dieseltravis/travis-ergogen-2026/datasheets/mcu-Liatris-rev1.0.webp

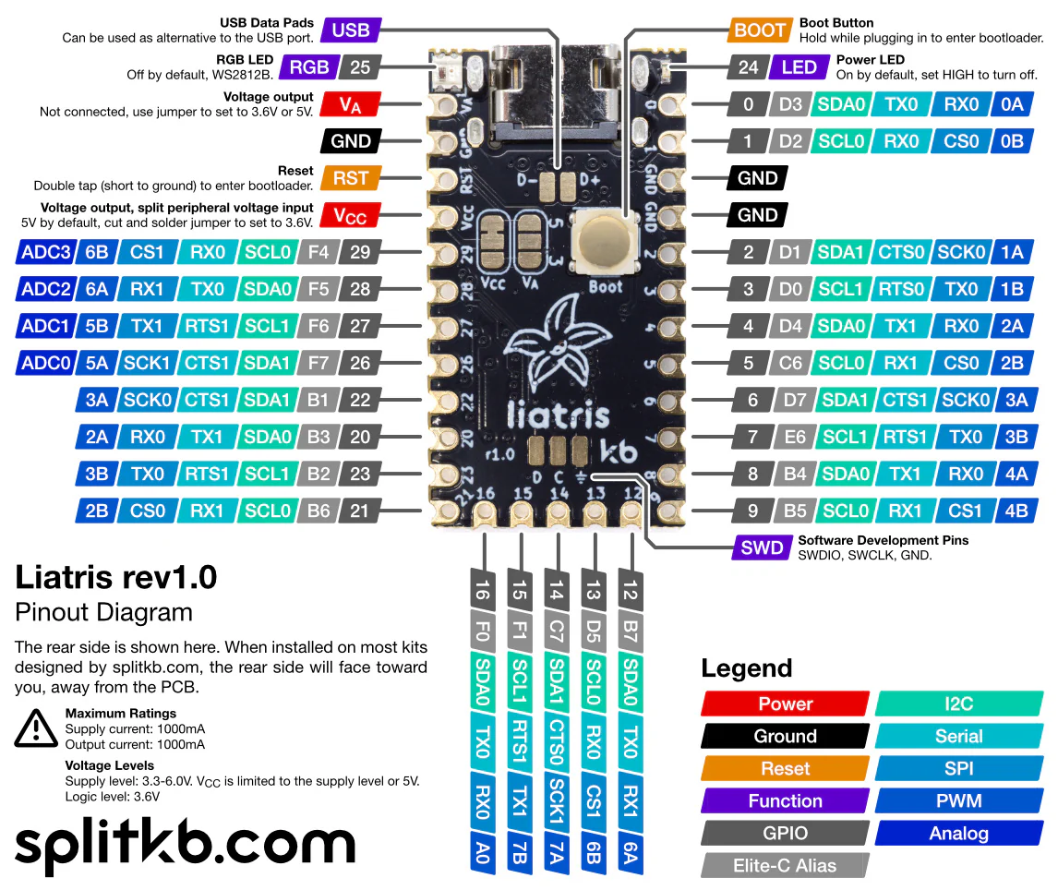
datasheets/mcu-Liatris-rev1.0.webp
