dieseltravis/travis-ergogen-2026/output/outlines/_2u_stabilizer.dxf

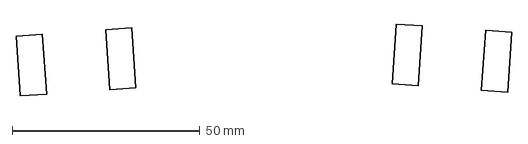
[picture p21: CAD file, 2026-01-18]
output/outlines/_2u_stabilizer.dxf
132.0 x 19.2 mm
