dieseltravis/travis-ergogen-2026/output/outlines/_keys.dxf

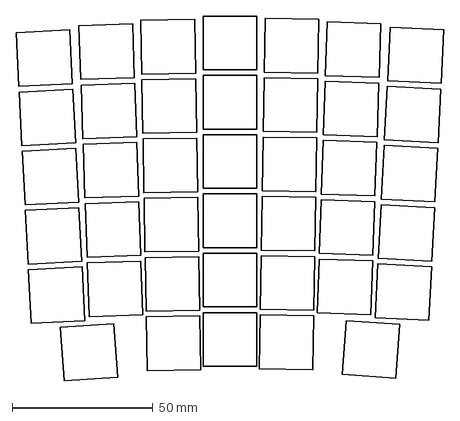
[picture p22: CAD file, 2026-01-15]
output/outlines/_keys.dxf
151.8 x 129.5 mm
