dieseltravis/travis-ergogen-2026/output/points/points.yaml

matrix_col0_row0:
    x: 60.0112611
    'y': -199.475332
    r: 4
    meta:
        stagger: 0
        spread: 20.05
        splay: 3
        origin:
            - 0
            - 0
        orient: 0
        shift:
            - 10.025
            - 0
        rotate: 1
        adjust: {}
        width: 38.1
        height: 18
        padding: 21.05
        autobind: 10
        skip: false
        asym: both
        colrow: col0_row0
        name: matrix_col0_row0
        tags:
            - row_even
            - key
            - 2u_stabs
        column_net: col0
        row_net: row0
        key:
            led_next: LED37
            led_this: LED36
        zone:
            key:
                padding: kp
                spread: kspr
                tags:
                    - key
            columns:
                col0:
                    key:
                        tags: col_even
                        splay: 3sp
                        stagger: 0st
                        column_net: col0
                    rows:
                        row0:
                            shift:
                                - 0.5kspr
                                - 0.0kp
                            width: 2U
                            rotate: 1
                            tags:
                                - row_even
                                - key
                                - 2u_stabs
                            key:
                                led_next: LED37
                                led_this: LED36
                        row1:
                            shift:
                                - '-0.5kspr'
                                - 0.0kp
                            rotate: -1
                            key:
                                led_next: LED36
                                led_this: LED35
                        row2:
                            key:
                                led_next: LED23
                                led_this: LED22
                        row3:
                            key:
                                led_next: LED22
                                led_this: LED21
                        row4:
                            key:
                                led_next: LED09
                                led_this: LED08
                        row5:
                            key:
                                led_next: LED08
                                led_this: LED07
                    name: col0
                col1:
                    key:
                        tags: col_odd
                        splay: '-sp'
                        stagger: st
                        column_net: col1
                    rows:
                        row0:
                            skip: true
                        row1:
                            key:
                                led_next: LED35
                                led_this: LED34
                        row2:
                            key:
                                led_next: LED24
                                led_this: LED23
                        row3:
                            key:
                                led_next: LED21
                                led_this: LED20
                        row4:
                            key:
                                led_next: LED10
                                led_this: LED09
                        row5:
                            key:
                                led_next: LED07
                                led_this: LED06
                    name: col1
                col2:
                    key:
                        tags: col_even
                        splay: '-sp'
                        stagger: st
                        column_net: col2
                    rows:
                        row0:
                            key:
                                led_next: LED38
                                led_this: LED37
                        row1:
                            key:
                                led_next: LED34
                                led_this: LED33
                        row2:
                            key:
                                led_next: LED25
                                led_this: LED24
                        row3:
                            key:
                                led_next: LED20
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
                    shift:
                        - '-0.5kspr'
                        - 0.0kp
                    rotate: -1
                    key:
                        led_next: LED36
                        led_this: LED35
                row2:
                    key:
                        led_next: LED23
                        led_this: LED22
                row3:
                    key:
                        led_next: LED22
                        led_this: LED21
                row4:
                    key:
                        led_next: LED09
                        led_this: LED08
                row5:
                    key:
                        led_next: LED08
                        led_this: LED07
            name: col0
        row: row0
        bind:
            - 10
            - 0
            - 0
            - 0
matrix_col0_row1:
    x: 48.542307699999995
    'y': -179.1759173
    r: 3
    meta:
        stagger: 0
        spread: 20.05
        splay: 3
        origin:
            - 0
            - 0
        orient: 0
        shift:
            - -10.025
            - 0
        rotate: -1
        adjust: {}
        width: 18
        height: 18
        padding: 21.05
        autobind: 10
        skip: false
        asym: both
        colrow: col0_row1
        name: matrix_col0_row1
        tags:
            - key
            - row_odd
        column_net: col0
        row_net: row1
        key:
            led_next: LED36
            led_this: LED35
        zone:
            key:
                padding: kp
                spread: kspr
                tags:
                    - key
            columns:
                col0:
                    key:
                        tags: col_even
                        splay: 3sp
                        stagger: 0st
                        column_net: col0
                    rows:
                        row0:
                            shift:
                                - 0.5kspr
                                - 0.0kp
                            width: 2U
                            rotate: 1
                            tags:
                                - row_even
                                - key
                                - 2u_stabs
                            key:
                                led_next: LED37
                                led_this: LED36
                        row1:
                            shift:
                                - '-0.5kspr'
                                - 0.0kp
                            rotate: -1
                            key:
                                led_next: LED36
                                led_this: LED35
                        row2:
                            key:
                                led_next: LED23
                                led_this: LED22
                        row3:
                            key:
                                led_next: LED22
                                led_this: LED21
                        row4:
                            key:
                                led_next: LED09
                                led_this: LED08
                        row5:
                            key:
                                led_next: LED08
                                led_this: LED07
                    name: col0
                col1:
                    key:
                        tags: col_odd
                        splay: '-sp'
                        stagger: st
                        column_net: col1
                    rows:
                        row0:
                            skip: true
                        row1:
                            key:
                                led_next: LED35
                                led_this: LED34
                        row2:
                            key:
                                led_next: LED24
                                led_this: LED23
                        row3:
                            key:
                                led_next: LED21
                                led_this: LED20
                        row4:
                            key:
                                led_next: LED10
                                led_this: LED09
                        row5:
                            key:
                                led_next: LED07
                                led_this: LED06
                    name: col1
                col2:
                    key:
                        tags: col_even
                        splay: '-sp'
                        stagger: st
                        column_net: col2
                    rows:
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
                        row4:
                            key:
                                led_next: LED14
                                led_this: LED13
                        row5:
                            key:
                                led_next: LED03
                                led_this: LED02
                    name: col5
                col6:
                    key:
                        tags: col_even
                        splay: '-sp'
                        stagger: '-st'
                        column_net: col6
                    rows:
                        row0:
                            shift:
                                - '-0.5kspr'
                                - 0.0kp
                            width: 2U
                            rotate: -1
                            tags:
                                - row_even
                                - key
                                - 2u_stabs
                            key:
                                led_next: ''
                                led_this: LED40
                        row1:
                            shift:
                                - 0.5kspr
                                - 0.0kp
                            rotate: 1
                            key:
                                led_next: LED30
                                led_this: LED29
                        row2:
                            key:
                                led_next: LED29
                                led_this: LED28
                        row3:
                            key:
                                led_next: LED16
                                led_this: LED15
                        row4:
                            key:
                                led_next: LED15
                                led_this: LED14
                        row5:
                            key:
                                led_next: LED02
                                led_this: LED01
                    name: col6
            rows:
                row0:
                    tags:
                        - key
                        - row_even
                    row_net: row0
                row1:
                    tags:
                        - key
                        - row_odd
                    row_net: row1
                row2:
                    tags:
                        - key
                        - row_even
                    row_net: row2
                row3:
                    tags:
                        - key
                        - row_odd
                    row_net: row3
                row4:
                    tags:
                        - key
                        - row_even
                    row_net: row4
                row5:
                    tags:
                        - key
                        - row_odd
                    row_net: row5
            name: matrix
        col:
            key:
                tags: col_even
                splay: 3sp
                stagger: 0st
                column_net: col0
            rows:
                row0:
                    shift:
                        - 0.5kspr
                        - 0.0kp
                    width: 2U
                    rotate: 1
                    tags:
                        - row_even
                        - key
                        - 2u_stabs
                    key:
                        led_next: LED37
                        led_this: LED36
                row1:
                    shift:
                        - '-0.5kspr'
                        - 0.0kp
                    rotate: -1
                    key:
                        led_next: LED36
                        led_this: LED35
                row2:
                    key:
                        led_next: LED23
                        led_this: LED22
                row3:
                    key:
                        led_next: LED22
                        led_this: LED21
                row4:
                    key:
                        led_next: LED09
                        led_this: LED08
                row5:
                    key:
                        led_next: LED08
                        led_this: LED07
            name: col0
        row: row1
        bind:
            - 10
            - 0
            - 10
            - 0
matrix_col0_row2:
    x: 47.440635799999995
    'y': -158.15476560000002
    r: 3
    meta:
        stagger: 0
        spread: 20.05
        splay: 3
        origin:
            - 0
            - 0
        orient: 0
        shift:
            - 0
            - 0
        rotate: 0
        adjust: {}
        width: 18
        height: 18
        padding: 21.05
        autobind: 10
        skip: false
        asym: both
        colrow: col0_row2
        name: matrix_col0_row2
        tags:
            - key
            - row_even
        column_net: col0
        row_net: row2
        key:
            led_next: LED23
            led_this: LED22
        zone:
            key:
                padding: kp
                spread: kspr
                tags:
                    - key
            columns:
                col0:
                    key:
                        tags: col_even
                        splay: 3sp
                        stagger: 0st
                        column_net: col0
                    rows:
                        row0:
                            shift:
                                - 0.5kspr
                                - 0.0kp
                            width: 2U
                            rotate: 1
                            tags:
                                - row_even
                                - key
                                - 2u_stabs
                            key:
                                led_next: LED37
                                led_this: LED36
                        row1:
                            shift:
                                - '-0.5kspr'
                                - 0.0kp
                            rotate: -1
                            key:
                                led_next: LED36
                                led_this: LED35
                        row2:
                            key:
                                led_next: LED23
                                led_this: LED22
                        row3:
                            key:
                                led_next: LED22
                                led_this: LED21
                        row4:
                            key:
                                led_next: LED09
                                led_this: LED08
                        row5:
                            key:
                                led_next: LED08
                                led_this: LED07
                    name: col0
                col1:
                    key:
                        tags: col_odd
                        splay: '-sp'
                        stagger: st
                        column_net: col1
                    rows:
                        row0:
                            skip: true
                        row1:
                            key:
                                led_next: LED35
                                led_this: LED34
                        row2:
                            key:
                                led_next: LED24
                                led_this: LED23
                        row3:
                            key:
                                led_next: LED21
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
                        stagger: '-st'
                        column_net: col5
                    rows:
                        row0:
                            skip: true
                        row1:
                            key:
                                led_next: LED31
                                led_this: LED30
                        row2:
                            key:
                                led_next: LED28
                                led_this: LED27
                        row3:
                            key:
                                led_next: LED17
                                led_this: LED16
                        row4:
                            key:
                                led_next: LED14
                                led_this: LED13
                        row5:
                            key:
                                led_next: LED03
                                led_this: LED02
                    name: col5
                col6:
                    key:
                        tags: col_even
                        splay: '-sp'
                        stagger: '-st'
                        column_net: col6
                    rows:
                        row0:
                            shift:
                                - '-0.5kspr'
                                - 0.0kp
                            width: 2U
                            rotate: -1
                            tags:
                                - row_even
                                - key
                                - 2u_stabs
                            key:
                                led_next: ''
                                led_this: LED40
                        row1:
                            shift:
                                - 0.5kspr
                                - 0.0kp
                            rotate: 1
                            key:
                                led_next: LED30
                                led_this: LED29
                        row2:
                            key:
                                led_next: LED29
                                led_this: LED28
                        row3:
                            key:
                                led_next: LED16
                                led_this: LED15
                        row4:
                            key:
                                led_next: LED15
                                led_this: LED14
                        row5:
                            key:
                                led_next: LED02
                                led_this: LED01
                    name: col6
            rows:
                row0:
                    tags:
                        - key
                        - row_even
                    row_net: row0
                row1:
                    tags:
                        - key
                        - row_odd
                    row_net: row1
                row2:
                    tags:
                        - key
                        - row_even
                    row_net: row2
                row3:
                    tags:
                        - key
                        - row_odd
                    row_net: row3
                row4:
                    tags:
                        - key
                        - row_even
                    row_net: row4
                row5:
                    tags:
                        - key
                        - row_odd
                    row_net: row5
            name: matrix
        col:
            key:
                tags: col_even
                splay: 3sp
                stagger: 0st
                column_net: col0
            rows:
                row0:
                    shift:
                        - 0.5kspr
                        - 0.0kp
                    width: 2U
                    rotate: 1
                    tags:
                        - row_even
                        - key
                        - 2u_stabs
                    key:
                        led_next: LED37
                        led_this: LED36
                row1:
                    shift:
                        - '-0.5kspr'
                        - 0.0kp
                    rotate: -1
                    key:
                        led_next: LED36
                        led_this: LED35
                row2:
                    key:
                        led_next: LED23
                        led_this: LED22
                row3:
                    key:
                        led_next: LED22
                        led_this: LED21
                row4:
                    key:
                        led_next: LED09
                        led_this: LED08
                row5:
                    key:
                        led_next: LED08
                        led_this: LED07
            name: col0
        row: row2
        bind:
            - 10
            - 10
            - 10
            - 0
matrix_col0_row3:
    x: 46.338963899999996
    'y': -137.13361390000003
    r: 3
    meta:
        stagger: 0
        spread: 20.05
        splay: 3
        origin:
            - 0
            - 0
        orient: 0
        shift:
            - 0
            - 0
        rotate: 0
        adjust: {}
        width: 18
        height: 18
        padding: 21.05
        autobind: 10
        skip: false
        asym: both
        colrow: col0_row3
        name: matrix_col0_row3
        tags:
            - key
            - row_odd
        column_net: col0
        row_net: row3
        key:
            led_next: LED22
            led_this: LED21
        zone:
            key:
                padding: kp
                spread: kspr
                tags:
                    - key
            columns:
                col0:
                    key:
                        tags: col_even
                        splay: 3sp
                        stagger: 0st
                        column_net: col0
                    rows:
                        row0:
                            shift:
                                - 0.5kspr
                                - 0.0kp
                            width: 2U
                            rotate: 1
                            tags:
                                - row_even
                                - key
                                - 2u_stabs
                            key:
                                led_next: LED37
                                led_this: LED36
                        row1:
                            shift:
                                - '-0.5kspr'
                                - 0.0kp
                            rotate: -1
                            key:
                                led_next: LED36
                                led_this: LED35
                        row2:
                            key:
                                led_next: LED23
                                led_this: LED22
                        row3:
                            key:
                                led_next: LED22
                                led_this: LED21
                        row4:
                            key:
                                led_next: LED09
                                led_this: LED08
                        row5:
                            key:
                                led_next: LED08
                                led_this: LED07
                    name: col0
                col1:
                    key:
                        tags: col_odd
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
                            key:
                                led_next: LED18
                                led_this: LED17
                        row4:
                            key:
                                led_next: LED13
                                led_this: LED12
                        row5:
                            key:
                                led_next: LED04
                                led_this: LED03
                    name: col4
                col5:
                    key:
                        tags: col_odd
                        splay: '-sp'
                        stagger: '-st'
                        column_net: col5
                    rows:
                        row0:
                            skip: true
                        row1:
                            key:
                                led_next: LED31
                                led_this: LED30
                        row2:
                            key:
                                led_next: LED28
                                led_this: LED27
                        row3:
                            key:
                                led_next: LED17
                                led_this: LED16
                        row4:
                            key:
                                led_next: LED14
                                led_this: LED13
                        row5:
                            key:
                                led_next: LED03
                                led_this: LED02
                    name: col5
                col6:
                    key:
                        tags: col_even
                        splay: '-sp'
                        stagger: '-st'
                        column_net: col6
                    rows:
                        row0:
                            shift:
                                - '-0.5kspr'
                                - 0.0kp
                            width: 2U
                            rotate: -1
                            tags:
                                - row_even
                                - key
                                - 2u_stabs
                            key:
                                led_next: ''
                                led_this: LED40
                        row1:
                            shift:
                                - 0.5kspr
                                - 0.0kp
                            rotate: 1
                            key:
                                led_next: LED30
                                led_this: LED29
                        row2:
                            key:
                                led_next: LED29
                                led_this: LED28
                        row3:
                            key:
                                led_next: LED16
                                led_this: LED15
                        row4:
                            key:
                                led_next: LED15
                                led_this: LED14
                        row5:
                            key:
                                led_next: LED02
                                led_this: LED01
                    name: col6
            rows:
                row0:
                    tags:
                        - key
                        - row_even
                    row_net: row0
                row1:
                    tags:
                        - key
                        - row_odd
                    row_net: row1
                row2:
                    tags:
                        - key
                        - row_even
                    row_net: row2
                row3:
                    tags:
                        - key
                        - row_odd
                    row_net: row3
                row4:
                    tags:
                        - key
                        - row_even
                    row_net: row4
                row5:
                    tags:
                        - key
                        - row_odd
                    row_net: row5
            name: matrix
        col:
            key:
                tags: col_even
                splay: 3sp
                stagger: 0st
                column_net: col0
            rows:
                row0:
                    shift:
                        - 0.5kspr
                        - 0.0kp
                    width: 2U
                    rotate: 1
                    tags:
                        - row_even
                        - key
                        - 2u_stabs
                    key:
                        led_next: LED37
                        led_this: LED36
                row1:
                    shift:
                        - '-0.5kspr'
                        - 0.0kp
                    rotate: -1
                    key:
                        led_next: LED36
                        led_this: LED35
                row2:
                    key:
                        led_next: LED23
                        led_this: LED22
                row3:
                    key:
                        led_next: LED22
                        led_this: LED21
                row4:
                    key:
                        led_next: LED09
                        led_this: LED08
                row5:
                    key:
                        led_next: LED08
                        led_this: LED07
            name: col0
        row: row3
        bind:
            - 10
            - 10
            - 10
            - 0
matrix_col0_row4:
    x: 45.237292
    'y': -116.11246220000002
    r: 3
    meta:
        stagger: 0
        spread: 20.05
        splay: 3
        origin:
            - 0
            - 0
        orient: 0
        shift:
            - 0
            - 0
        rotate: 0
        adjust: {}
        width: 18
        height: 18
        padding: 21.05
        autobind: 10
        skip: false
        asym: both
        colrow: col0_row4
        name: matrix_col0_row4
        tags:
            - key
            - row_even
        column_net: col0
        row_net: row4
        key:
            led_next: LED09
            led_this: LED08
        zone:
            key:
                padding: kp
                spread: kspr
                tags:
                    - key
            columns:
                col0:
                    key:
                        tags: col_even
                        splay: 3sp
                        stagger: 0st
                        column_net: col0
                    rows:
                        row0:
                            shift:
                                - 0.5kspr
                                - 0.0kp
                            width: 2U
                            rotate: 1
                            tags:
                                - row_even
                                - key
                                - 2u_stabs
                            key:
                                led_next: LED37
                                led_this: LED36
                        row1:
                            shift:
                                - '-0.5kspr'
                                - 0.0kp
                            rotate: -1
                            key:
                                led_next: LED36
                                led_this: LED35
                        row2:
                            key:
                                led_next: LED23
                                led_this: LED22
                        row3:
                            key:
                                led_next: LED22
                                led_this: LED21
                        row4:
                            key:
                                led_next: LED09
                                led_this: LED08
                        row5:
                            key:
                                led_next: LED08
                                led_this: LED07
                    name: col0
                col1:
                    key:
                        tags: col_odd
                        splay: '-sp'
                        stagger: st
                        column_net: col1
                    rows:
                        row0:
                            skip: true
                        row1:
                            key:
                                led_next: LED35
                                led_this: LED34
                        row2:
                            key:
                                led_next: LED24
                                led_this: LED23
                        row3:
                            key:
                                led_next: LED21
                                led_this: LED20
                        row4:
                            key:
                                led_next: LED10
                                led_this: LED09
                        row5:
                            key:
                                led_next: LED07
                                led_this: LED06
                    name: col1
                col2:
                    key:
                        tags: col_even
                        splay: '-sp'
                        stagger: st
                        column_net: col2
                    rows:
                        row0:
                            key:
                                led_next: LED38
                                led_this: LED37
                        row1:
                            key:
                                led_next: LED34
                                led_this: LED33
                        row2:
                            key:
                                led_next: LED25
                                led_this: LED24
                        row3:
                            key:
                                led_next: LED20
                                led_this: LED19
                        row4:
                            key:
                                led_next: LED11
                                led_this: LED10
                        row5:
                            key:
                                led_next: LED06
                                led_this: LED05
                    name: col2
                col3:
                    key:
                        tags: col_odd
                        splay: '-sp'
                        stagger: st
                        column_net: col3
                    rows:
                        row0:
                            key:
                                led_next: LED39
                                led_this: LED38
                        row1:
                            key:
                                led_next: LED33
                                led_this: LED32
                        row2:
                            key:
                                led_next: LED26
                                led_this: LED25
                        row3:
                            key:
                                led_next: LED19
                                led_this: LED18
                        row4:
                            key:
                                led_next: LED12
                                led_this: LED11
                        row5:
                            key:
                                led_next: LED05
                                led_this: LED04
                    name: col3
                col4:
                    key:
                        tags: col_even
                        splay: '-sp'
                        stagger: '-st'
                        column_net: col4
                    rows:
                        row0:
                            key:
                                led_next: LED40
                                led_this: LED39
                        row1:
                            key:
                                led_next: LED32
                                led_this: LED31
                        row2:
                            key:
                                led_next: LED27
                                led_this: LED26
                        row3:
                            key:
                                led_next: LED18
                                led_this: LED17
                        row4:
                            key:
                                led_next: LED13
                                led_this: LED12
                        row5:
                            key:
                                led_next: LED04
                                led_this: LED03
                    name: col4
                col5:
                    key:
                        tags: col_odd
                        splay: '-sp'
                        stagger: '-st'
                        column_net: col5
                    rows:
                        row0:
                            skip: true
                        row1:
                            key:
                                led_next: LED31
                                led_this: LED30
                        row2:
                            key:
                                led_next: LED28
                                led_this: LED27
                        row3:
                            key:
                                led_next: LED17
                                led_this: LED16
                        row4:
                            key:
                                led_next: LED14
                                led_this: LED13
                        row5:
                            key:
                                led_next: LED03
                                led_this: LED02
                    name: col5
                col6:
                    key:
                        tags: col_even
                        splay: '-sp'
                        stagger: '-st'
                        column_net: col6
                    rows:
                        row0:
                            shift:
                                - '-0.5kspr'
                                - 0.0kp
                            width: 2U
                            rotate: -1
                            tags:
                                - row_even
                                - key
                                - 2u_stabs
                            key:
                                led_next: ''
                                led_this: LED40
                        row1:
                            shift:
                                - 0.5kspr
                                - 0.0kp
                            rotate: 1
                            key:
                                led_next: LED30
                                led_this: LED29
                        row2:
                            key:
                                led_next: LED29
                                led_this: LED28
                        row3:
                            key:
                                led_next: LED16
                                led_this: LED15
                        row4:
                            key:
                                led_next: LED15
                                led_this: LED14
                        row5:
                            key:
                                led_next: LED02
                                led_this: LED01
                    name: col6
            rows:
                row0:
                    tags:
                        - key
                        - row_even
                    row_net: row0
                row1:
                    tags:
                        - key
                        - row_odd
                    row_net: row1
                row2:
                    tags:
                        - key
                        - row_even
                    row_net: row2
                row3:
                    tags:
                        - key
                        - row_odd
                    row_net: row3
                row4:
                    tags:
                        - key
                        - row_even
                    row_net: row4
                row5:
                    tags:
                        - key
                        - row_odd
                    row_net: row5
            name: matrix
        col:
            key:
                tags: col_even
                splay: 3sp
                stagger: 0st
                column_net: col0
            rows:
                row0:
                    shift:
                        - 0.5kspr
                        - 0.0kp
                    width: 2U
                    rotate: 1
                    tags:
                        - row_even
                        - key
                        - 2u_stabs
                    key:
                        led_next: LED37
                        led_this: LED36
                row1:
                    shift:
                        - '-0.5kspr'
                        - 0.0kp
                    rotate: -1
                    key:
                        led_next: LED36
                        led_this: LED35
                row2:
                    key:
                        led_next: LED23
                        led_this: LED22
                row3:
                    key:
                        led_next: LED22
                        led_this: LED21
                row4:
                    key:
                        led_next: LED09
                        led_this: LED08
                row5:
                    key:
                        led_next: LED08
                        led_this: LED07
            name: col0
        row: row4
        bind:
            - 10
            - 10
            - 10
            - 0
matrix_col0_row5:
    x: 44.1356201
    'y': -95.09131050000002
    r: 3
    meta:
        stagger: 0
        spread: 20.05
        splay: 3
        origin:
            - 0
            - 0
        orient: 0
        shift:
            - 0
            - 0
        rotate: 0
        adjust: {}
        width: 18
        height: 18
        padding: 21.05
        autobind: 10
        skip: false
        asym: both
        colrow: col0_row5
        name: matrix_col0_row5
        tags:
            - key
            - row_odd
        column_net: col0
        row_net: row5
        key:
            led_next: LED08
            led_this: LED07
        zone:
            key:
                padding: kp
                spread: kspr
                tags:
                    - key
            columns:
                col0:
                    key:
                        tags: col_even
                        splay: 3sp
                        stagger: 0st
                        column_net: col0
                    rows:
                        row0:
                            shift:
                                - 0.5kspr
                                - 0.0kp
                            width: 2U
                            rotate: 1
                            tags:
                                - row_even
                                - key
                                - 2u_stabs
                            key:
                                led_next: LED37
                                led_this: LED36
                        row1:
                            shift:
                                - '-0.5kspr'
                                - 0.0kp
                            rotate: -1
                            key:
                                led_next: LED36
                                led_this: LED35
                        row2:
                            key:
                                led_next: LED23
                                led_this: LED22
                        row3:
                            key:
                                led_next: LED22
                                led_this: LED21
                        row4:
                            key:
                                led_next: LED09
                                led_this: LED08
                        row5:
                            key:
                                led_next: LED08
                                led_this: LED07
                    name: col0
                col1:
                    key:
                        tags: col_odd
                        splay: '-sp'
                        stagger: st
                        column_net: col1
                    rows:
                        row0:
                            skip: true
                        row1:
                            key:
                                led_next: LED35
                                led_this: LED34
                        row2:
                            key:
                                led_next: LED24
                                led_this: LED23
                        row3:
                            key:
                                led_next: LED21
                                led_this: LED20
                        row4:
                            key:
                                led_next: LED10
                                led_this: LED09
                        row5:
                            key:
                                led_next: LED07
                                led_this: LED06
                    name: col1
                col2:
                    key:
                        tags: col_even
                        splay: '-sp'
                        stagger: st
                        column_net: col2
                    rows:
                        row0:
                            key:
                                led_next: LED38
                                led_this: LED37
                        row1:
                            key:
                                led_next: LED34
                                led_this: LED33
                        row2:
                            key:
                                led_next: LED25
                                led_this: LED24
                        row3:
                            key:
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
                        led_this: LED36
                row1:
                    shift:
                        - '-0.5kspr'
                        - 0.0kp
                    rotate: -1
                    key:
                        led_next: LED36
                        led_this: LED35
                row2:
                    key:
                        led_next: LED23
                        led_this: LED22
                row3:
                    key:
                        led_next: LED22
                        led_this: LED21
                row4:
                    key:
                        led_next: LED09
                        led_this: LED08
                row5:
                    key:
                        led_next: LED08
                        led_this: LED07
            name: col0
        row: row5
        bind:
            - 0
            - 10
            - 10
            - 0
matrix_col1_row1:
    x: 69.2355518
    'y': -176.9148576
    r: 2
    meta:
        stagger: 1
        spread: 20.05
        splay: -1
        origin:
            - 0
            - 0
        orient: 0
        shift:
            - 0
            - 0
        rotate: 0
        adjust: {}
        width: 18
        height: 18
        padding: 21.05
        autobind: 10
        skip: false
        asym: both
        colrow: col1_row1
        name: matrix_col1_row1
        tags:
            - key
            - row_odd
        column_net: col1
        row_net: row1
        key:
            led_next: LED35
            led_this: LED34
        zone:
            key:
                padding: kp
                spread: kspr
                tags:
                    - key
            columns:
                col0:
                    key:
                        tags: col_even
                        splay: 3sp
                        stagger: 0st
                        column_net: col0
                    rows:
                        row0:
                            shift:
                                - 0.5kspr
                                - 0.0kp
                            width: 2U
                            rotate: 1
                            tags:
                                - row_even
                                - key
                                - 2u_stabs
                            key:
                                led_next: LED37
                                led_this: LED36
                        row1:
                            shift:
                                - '-0.5kspr'
                                - 0.0kp
                            rotate: -1
                            key:
                                led_next: LED36
                                led_this: LED35
                        row2:
                            key:
                                led_next: LED23
                                led_this: LED22
                        row3:
                            key:
                                led_next: LED22
                                led_this: LED21
                        row4:
                            key:
                                led_next: LED09
                                led_this: LED08
                        row5:
                            key:
                                led_next: LED08
                                led_this: LED07
                    name: col0
                col1:
                    key:
                        tags: col_odd
                        splay: '-sp'
                        stagger: st
                        column_net: col1
                    rows:
                        row0:
                            skip: true
                        row1:
                            key:
                                led_next: LED35
                                led_this: LED34
                        row2:
                            key:
                                led_next: LED24
                                led_this: LED23
                        row3:
                            key:
                                led_next: LED21
                                led_this: LED20
                        row4:
                            key:
                                led_next: LED10
                                led_this: LED09
                        row5:
                            key:
                                led_next: LED07
                                led_this: LED06
                    name: col1
                col2:
                    key:
                        tags: col_even
                        splay: '-sp'
                        stagger: st
                        column_net: col2
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
                        row4:
                            key:
                                led_next: LED14
                                led_this: LED13
                        row5:
                            key:
                                led_next: LED03
                                led_this: LED02
                    name: col5
                col6:
                    key:
                        tags: col_even
                        splay: '-sp'
                        stagger: '-st'
                        column_net: col6
                    rows:
                        row0:
                            shift:
                                - '-0.5kspr'
                                - 0.0kp
                            width: 2U
                            rotate: -1
                            tags:
                                - row_even
                                - key
                                - 2u_stabs
                            key:
                                led_next: ''
                                led_this: LED40
                        row1:
                            shift:
                                - 0.5kspr
                                - 0.0kp
                            rotate: 1
                            key:
                                led_next: LED30
                                led_this: LED29
                        row2:
                            key:
                                led_next: LED29
                                led_this: LED28
                        row3:
                            key:
                                led_next: LED16
                                led_this: LED15
                        row4:
                            key:
                                led_next: LED15
                                led_this: LED14
                        row5:
                            key:
                                led_next: LED02
                                led_this: LED01
                    name: col6
            rows:
                row0:
                    tags:
                        - key
                        - row_even
                    row_net: row0
                row1:
                    tags:
                        - key
                        - row_odd
                    row_net: row1
                row2:
                    tags:
                        - key
                        - row_even
                    row_net: row2
                row3:
                    tags:
                        - key
                        - row_odd
                    row_net: row3
                row4:
                    tags:
                        - key
                        - row_even
                    row_net: row4
                row5:
                    tags:
                        - key
                        - row_odd
                    row_net: row5
            name: matrix
        col:
            key:
                tags: col_odd
                splay: '-sp'
                stagger: st
                column_net: col1
            rows:
                row0:
                    skip: true
                row1:
                    key:
                        led_next: LED35
                        led_this: LED34
                row2:
                    key:
                        led_next: LED24
                        led_this: LED23
                row3:
                    key:
                        led_next: LED21
                        led_this: LED20
                row4:
                    key:
                        led_next: LED10
                        led_this: LED09
                row5:
                    key:
                        led_next: LED07
                        led_this: LED06
            name: col1
        row: row1
        bind:
            - 10
            - 10
            - 0
            - 10
matrix_col1_row2:
    x: 68.50091739999999
    'y': -155.8776807
    r: 2
    meta:
        stagger: 1
        spread: 20.05
        splay: -1
        origin:
            - 0
            - 0
        orient: 0
        shift:
            - 0
            - 0
        rotate: 0
        adjust: {}
        width: 18
        height: 18
        padding: 21.05
        autobind: 10
        skip: false
        asym: both
        colrow: col1_row2
        name: matrix_col1_row2
        tags:
            - key
            - row_even
        column_net: col1
        row_net: row2
        key:
            led_next: LED24
            led_this: LED23
        zone:
            key:
                padding: kp
                spread: kspr
                tags:
                    - key
            columns:
                col0:
                    key:
                        tags: col_even
                        splay: 3sp
                        stagger: 0st
                        column_net: col0
                    rows:
                        row0:
                            shift:
                                - 0.5kspr
                                - 0.0kp
                            width: 2U
                            rotate: 1
                            tags:
                                - row_even
                                - key
                                - 2u_stabs
                            key:
                                led_next: LED37
                                led_this: LED36
                        row1:
                            shift:
                                - '-0.5kspr'
                                - 0.0kp
                            rotate: -1
                            key:
                                led_next: LED36
                                led_this: LED35
                        row2:
                            key:
                                led_next: LED23
                                led_this: LED22
                        row3:
                            key:
                                led_next: LED22
                                led_this: LED21
                        row4:
                            key:
                                led_next: LED09
                                led_this: LED08
                        row5:
                            key:
                                led_next: LED08
                                led_this: LED07
                    name: col0
                col1:
                    key:
                        tags: col_odd
                        splay: '-sp'
                        stagger: st
                        column_net: col1
                    rows:
                        row0:
                            skip: true
                        row1:
                            key:
                                led_next: LED35
                                led_this: LED34
                        row2:
                            key:
                                led_next: LED24
                                led_this: LED23
                        row3:
                            key:
                                led_next: LED21
                                led_this: LED20
                        row4:
                            key:
                                led_next: LED10
                                led_this: LED09
                        row5:
                            key:
                                led_next: LED07
                                led_this: LED06
                    name: col1
                col2:
                    key:
                        tags: col_even
                        splay: '-sp'
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
                                led_next: LED17
                                led_this: LED16
                        row4:
                            key:
                                led_next: LED14
                                led_this: LED13
                        row5:
                            key:
                                led_next: LED03
                                led_this: LED02
                    name: col5
                col6:
                    key:
                        tags: col_even
                        splay: '-sp'
                        stagger: '-st'
                        column_net: col6
                    rows:
                        row0:
                            shift:
                                - '-0.5kspr'
                                - 0.0kp
                            width: 2U
                            rotate: -1
                            tags:
                                - row_even
                                - key
                                - 2u_stabs
                            key:
                                led_next: ''
                                led_this: LED40
                        row1:
                            shift:
                                - 0.5kspr
                                - 0.0kp
                            rotate: 1
                            key:
                                led_next: LED30
                                led_this: LED29
                        row2:
                            key:
                                led_next: LED29
                                led_this: LED28
                        row3:
                            key:
                                led_next: LED16
                                led_this: LED15
                        row4:
                            key:
                                led_next: LED15
                                led_this: LED14
                        row5:
                            key:
                                led_next: LED02
                                led_this: LED01
                    name: col6
            rows:
                row0:
                    tags:
                        - key
                        - row_even
                    row_net: row0
                row1:
                    tags:
                        - key
                        - row_odd
                    row_net: row1
                row2:
                    tags:
                        - key
                        - row_even
                    row_net: row2
                row3:
                    tags:
                        - key
                        - row_odd
                    row_net: row3
                row4:
                    tags:
                        - key
                        - row_even
                    row_net: row4
                row5:
                    tags:
                        - key
                        - row_odd
                    row_net: row5
            name: matrix
        col:
            key:
                tags: col_odd
                splay: '-sp'
                stagger: st
                column_net: col1
            rows:
                row0:
                    skip: true
                row1:
                    key:
                        led_next: LED35
                        led_this: LED34
                row2:
                    key:
                        led_next: LED24
                        led_this: LED23
                row3:
                    key:
                        led_next: LED21
                        led_this: LED20
                row4:
                    key:
                        led_next: LED10
                        led_this: LED09
                row5:
                    key:
                        led_next: LED07
                        led_this: LED06
            name: col1
        row: row2
        bind:
            - 10
            - 10
            - 10
            - 10
matrix_col1_row3:
    x: 67.76628299999999
    'y': -134.84050380000002
    r: 2
    meta:
        stagger: 1
        spread: 20.05
        splay: -1
        origin:
            - 0
            - 0
        orient: 0
        shift:
            - 0
            - 0
        rotate: 0
        adjust: {}
        width: 18
        height: 18
        padding: 21.05
        autobind: 10
        skip: false
        asym: both
        colrow: col1_row3
        name: matrix_col1_row3
        tags:
            - key
            - row_odd
        column_net: col1
        row_net: row3
        key:
            led_next: LED21
            led_this: LED20
        zone:
            key:
                padding: kp
                spread: kspr
                tags:
                    - key
            columns:
                col0:
                    key:
                        tags: col_even
                        splay: 3sp
                        stagger: 0st
                        column_net: col0
                    rows:
                        row0:
                            shift:
                                - 0.5kspr
                                - 0.0kp
                            width: 2U
                            rotate: 1
                            tags:
                                - row_even
                                - key
                                - 2u_stabs
                            key:
                                led_next: LED37
                                led_this: LED36
                        row1:
                            shift:
                                - '-0.5kspr'
                                - 0.0kp
                            rotate: -1
                            key:
                                led_next: LED36
                                led_this: LED35
                        row2:
                            key:
                                led_next: LED23
                                led_this: LED22
                        row3:
                            key:
                                led_next: LED22
                                led_this: LED21
                        row4:
                            key:
                                led_next: LED09
                                led_this: LED08
                        row5:
                            key:
                                led_next: LED08
                                led_this: LED07
                    name: col0
                col1:
                    key:
                        tags: col_odd
                        splay: '-sp'
                        stagger: st
                        column_net: col1
                    rows:
                        row0:
                            skip: true
                        row1:
                            key:
                                led_next: LED35
                                led_this: LED34
                        row2:
                            key:
                                led_next: LED24
                                led_this: LED23
                        row3:
                            key:
                                led_next: LED21
                                led_this: LED20
                        row4:
                            key:
                                led_next: LED10
                                led_this: LED09
                        row5:
                            key:
                                led_next: LED07
                                led_this: LED06
                    name: col1
                col2:
                    key:
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
                        row3:
                            key:
                                led_next: LED17
                                led_this: LED16
                        row4:
                            key:
                                led_next: LED14
                                led_this: LED13
                        row5:
                            key:
                                led_next: LED03
                                led_this: LED02
                    name: col5
                col6:
                    key:
                        tags: col_even
                        splay: '-sp'
                        stagger: '-st'
                        column_net: col6
                    rows:
                        row0:
                            shift:
                                - '-0.5kspr'
                                - 0.0kp
                            width: 2U
                            rotate: -1
                            tags:
                                - row_even
                                - key
                                - 2u_stabs
                            key:
                                led_next: ''
                                led_this: LED40
                        row1:
                            shift:
                                - 0.5kspr
                                - 0.0kp
                            rotate: 1
                            key:
                                led_next: LED30
                                led_this: LED29
                        row2:
                            key:
                                led_next: LED29
                                led_this: LED28
                        row3:
                            key:
                                led_next: LED16
                                led_this: LED15
                        row4:
                            key:
                                led_next: LED15
                                led_this: LED14
                        row5:
                            key:
                                led_next: LED02
                                led_this: LED01
                    name: col6
            rows:
                row0:
                    tags:
                        - key
                        - row_even
                    row_net: row0
                row1:
                    tags:
                        - key
                        - row_odd
                    row_net: row1
                row2:
                    tags:
                        - key
                        - row_even
                    row_net: row2
                row3:
                    tags:
                        - key
                        - row_odd
                    row_net: row3
                row4:
                    tags:
                        - key
                        - row_even
                    row_net: row4
                row5:
                    tags:
                        - key
                        - row_odd
                    row_net: row5
            name: matrix
        col:
            key:
                tags: col_odd
                splay: '-sp'
                stagger: st
                column_net: col1
            rows:
                row0:
                    skip: true
                row1:
                    key:
                        led_next: LED35
                        led_this: LED34
                row2:
                    key:
                        led_next: LED24
                        led_this: LED23
                row3:
                    key:
                        led_next: LED21
                        led_this: LED20
                row4:
                    key:
                        led_next: LED10
                        led_this: LED09
                row5:
                    key:
                        led_next: LED07
                        led_this: LED06
            name: col1
        row: row3
        bind:
            - 10
            - 10
            - 10
            - 10
matrix_col1_row4:
    x: 67.03164859999998
    'y': -113.80332690000003
    r: 2
    meta:
        stagger: 1
        spread: 20.05
        splay: -1
        origin:
            - 0
            - 0
        orient: 0
        shift:
            - 0
            - 0
        rotate: 0
        adjust: {}
        width: 18
        height: 18
        padding: 21.05
        autobind: 10
        skip: false
        asym: both
        colrow: col1_row4
        name: matrix_col1_row4
        tags:
            - key
            - row_even
        column_net: col1
        row_net: row4
        key:
            led_next: LED10
            led_this: LED09
        zone:
            key:
                padding: kp
                spread: kspr
                tags:
                    - key
            columns:
                col0:
                    key:
                        tags: col_even
                        splay: 3sp
                        stagger: 0st
                        column_net: col0
                    rows:
                        row0:
                            shift:
                                - 0.5kspr
                                - 0.0kp
                            width: 2U
                            rotate: 1
                            tags:
                                - row_even
                                - key
                                - 2u_stabs
                            key:
                                led_next: LED37
                                led_this: LED36
                        row1:
                            shift:
                                - '-0.5kspr'
                                - 0.0kp
                            rotate: -1
                            key:
                                led_next: LED36
                                led_this: LED35
                        row2:
                            key:
                                led_next: LED23
                                led_this: LED22
                        row3:
                            key:
                                led_next: LED22
                                led_this: LED21
                        row4:
                            key:
                                led_next: LED09
                                led_this: LED08
                        row5:
                            key:
                                led_next: LED08
                                led_this: LED07
                    name: col0
                col1:
                    key:
                        tags: col_odd
                        splay: '-sp'
                        stagger: st
                        column_net: col1
                    rows:
                        row0:
                            skip: true
                        row1:
                            key:
                                led_next: LED35
                                led_this: LED34
                        row2:
                            key:
                                led_next: LED24
                                led_this: LED23
                        row3:
                            key:
                                led_next: LED21
                                led_this: LED20
                        row4:
                            key:
                                led_next: LED10
                                led_this: LED09
                        row5:
                            key:
                                led_next: LED07
                                led_this: LED06
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
                                led_next: LED28
                                led_this: LED27
                        row3:
                            key:
                                led_next: LED17
                                led_this: LED16
                        row4:
                            key:
                                led_next: LED14
                                led_this: LED13
                        row5:
                            key:
                                led_next: LED03
                                led_this: LED02
                    name: col5
                col6:
                    key:
                        tags: col_even
                        splay: '-sp'
                        stagger: '-st'
                        column_net: col6
                    rows:
                        row0:
                            shift:
                                - '-0.5kspr'
                                - 0.0kp
                            width: 2U
                            rotate: -1
                            tags:
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
