dieseltravis/travis-ergogen-2026/output/outlines/_combo.yaml

models:
    export:
        models:
            a:
                models:
                    a:
                        models: {}
                        origin:
                            - 0
                            - 0
                    b:
                        models:
                            a:
                                models: {}
                                origin:
                                    - 0
                                    - 0
                            b:
                                models:
                                    path1:
                                        paths:
                                            ShapeLine1:
                                                type: line
                                                origin:
                                                    - 177.9709487499303
                                                    - -59.57691364824681
                                                end:
                                                    - 187.26817242033962
                                                    - -60.06416051685221
                                            ShapeLine2:
                                                type: line
                                                origin:
                                                    - 191.99964009943398
                                                    - -65.31898821575624
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
                                                                                                                                                                                                                                                                                                            - 79.0871671
                                                                                                                                                                                                                                                                                                            - -186.1016375
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
