dieseltravis/travis-ergogen-2026/output/outlines/_pb.yaml

models:
    export:
        models:
            a:
                models: {}
                origin:
                    - 0
                    - 0
            b:
                paths:
                    p1:
                        type: line
                        origin:
                            - 40.73610242440432
                            - -186.4270106283559
                        end:
                            - 35.59631315758057
                            - -88.35399005041677
                    p2:
                        type: line
                        origin:
                            - 36.54260665758057
                            - -87.30302455041681
                        end:
                            - 50.597823847702905
                            - -86.56642186694972
                    p3:
                        type: line
                        origin:
                            - 50.747157147702886
                            - -86.54724606694971
                        end:
                            - 58.95841533550055
                            - -84.856549886339
                    p4:
                        type: line
                        origin:
                            - 59.12518513550055
                            - -84.836612786339
                        end:
                            - 72.91447932197943
                            - -84.35508000055316
                    p5:
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
                            - -208.74565082250717
                        radius: 1
                        startAngle: 184.00000130188937
                        endAngle: 274.00000130188687
                        type: arc
                    fillet26:
                        origin:
                            - 41.87546732195141
                            - -192.85779728310717
                        radius: 1
                        startAngle: 4.000001301882866
                        endAngle: 19.207654516054856
                        type: arc
                    fillet27:
                        origin:
                            - 41.734731924404336
                            - -186.37467462835602
                        radius: 1
                        startAngle: 183.0000026078682
                        endAngle: 199.20765451605484
                        type: arc
                origin:
                    - 0
                    - 0
        origin:
            - 0
            - 0
units: mm
origin:
    - 0
    - 0
