dieseltravis/travis-ergogen-2026/output/outlines/_standoff.yaml

models:
    export:
        models:
            a:
                models:
                    a:
                        models:
                            a:
                                models:
                                    a:
                                        models:
                                            a:
                                                models:
                                                    a:
                                                        models:
                                                            a:
                                                                models:
                                                                    a:
                                                                        models:
                                                                            a:
                                                                                models: {}
                                                                                origin:
                                                                                    - 0
                                                                                    - 0
                                                                            b:
                                                                                paths:
                                                                                    circle:
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
                                    - 112.8525666
                                    - -221.0593903
                            ShapeLine2:
                                type: line
                                origin:
                                    - 112.8525666
                                    - -221.0593903
                                end:
                                    - 112.8525666
                                    - -213.0593903
                            ShapeLine4:
                                type: line
                                origin:
                                    - 107.1525666
                                    - -213.0593903
                                end:
                                    - 107.1525666
                                    - -221.0593903
                        origin:
                            - 0
                            - 0
                origin:
                    - 0
                    - 0
            b:
                paths:
                    circle:
                        type: circle
                        origin:
                            - 44.9263753
                            - -213.8375862
                        radius: 2.85
                origin:
                    - 0
                    - 0
        origin:
            - 0
            - 0
units: mm
origin:
    - 0
    - 0
