dieseltravis/travis-ergogen-2026/output/outlines/_mounting.yaml

models:
    export:
        models:
            a:
                models:
                    a:
                        models:
                            a:
                                models:
                                    a:
                                        models:
                                            a:
                                                models:
                                                    a:
                                                        models: {}
                                                        origin:
                                                            - 0
                                                            - 0
                                                    b:
                                                        paths:
                                                            circle:
                                                                type: circle
                                                                origin:
                                                                    - 31.239265099999997
                                                                    - -64.44925970000003
                                                                radius: 1.5
                                                        origin:
                                                            - 0
                                                            - 0
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
                            - 44.9263753
                            - -213.8375862
                        radius: 1.5
                origin:
                    - 0
                    - 0
        origin:
            - 0
            - 0
units: mm
origin:
    - 0
    - 0
