dieseltravis/travis-ergogen-2026/output/points/units.yaml

U: 19.05
u: 19
cx: 18
cy: 17
$default_stagger: 0
$default_spread: 19
$default_splay: 0
$default_height: 18
$default_width: 18
$default_padding: 19
$default_autobind: 10
kp: 21.05
kspr: 20.05
bp: 14.525
sp: 1
st: 1
stabilizer_width: 7
stabilizer_height: 16
stabilizer_offset: 0
stabilizer_spacing_2u: 11.93
screwSize: 1.5
standoffSize: 2.85
board: 1.6
height: 4
wall: 2
casethick: 1
platehole: 13.95
platethick: 1.41
plate2uw: 15.43
platew: 1.2
